mage0r/Mitsubishi-ESPHome/Photos/2024-11-02 19.26.33.jpg

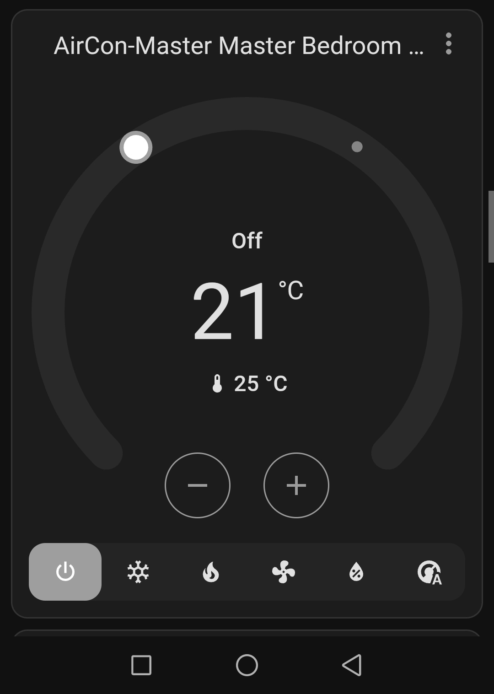
Photos/2024-11-02 19.26.33.jpg
